Monty103/MSBE_v3/hardware/kicad/ver_1.0/MSBE_V3.kicad_sch

## KiCad design hardware/kicad/ver_1.0/MSBE_V3.kicad_sch (2026-07-17)

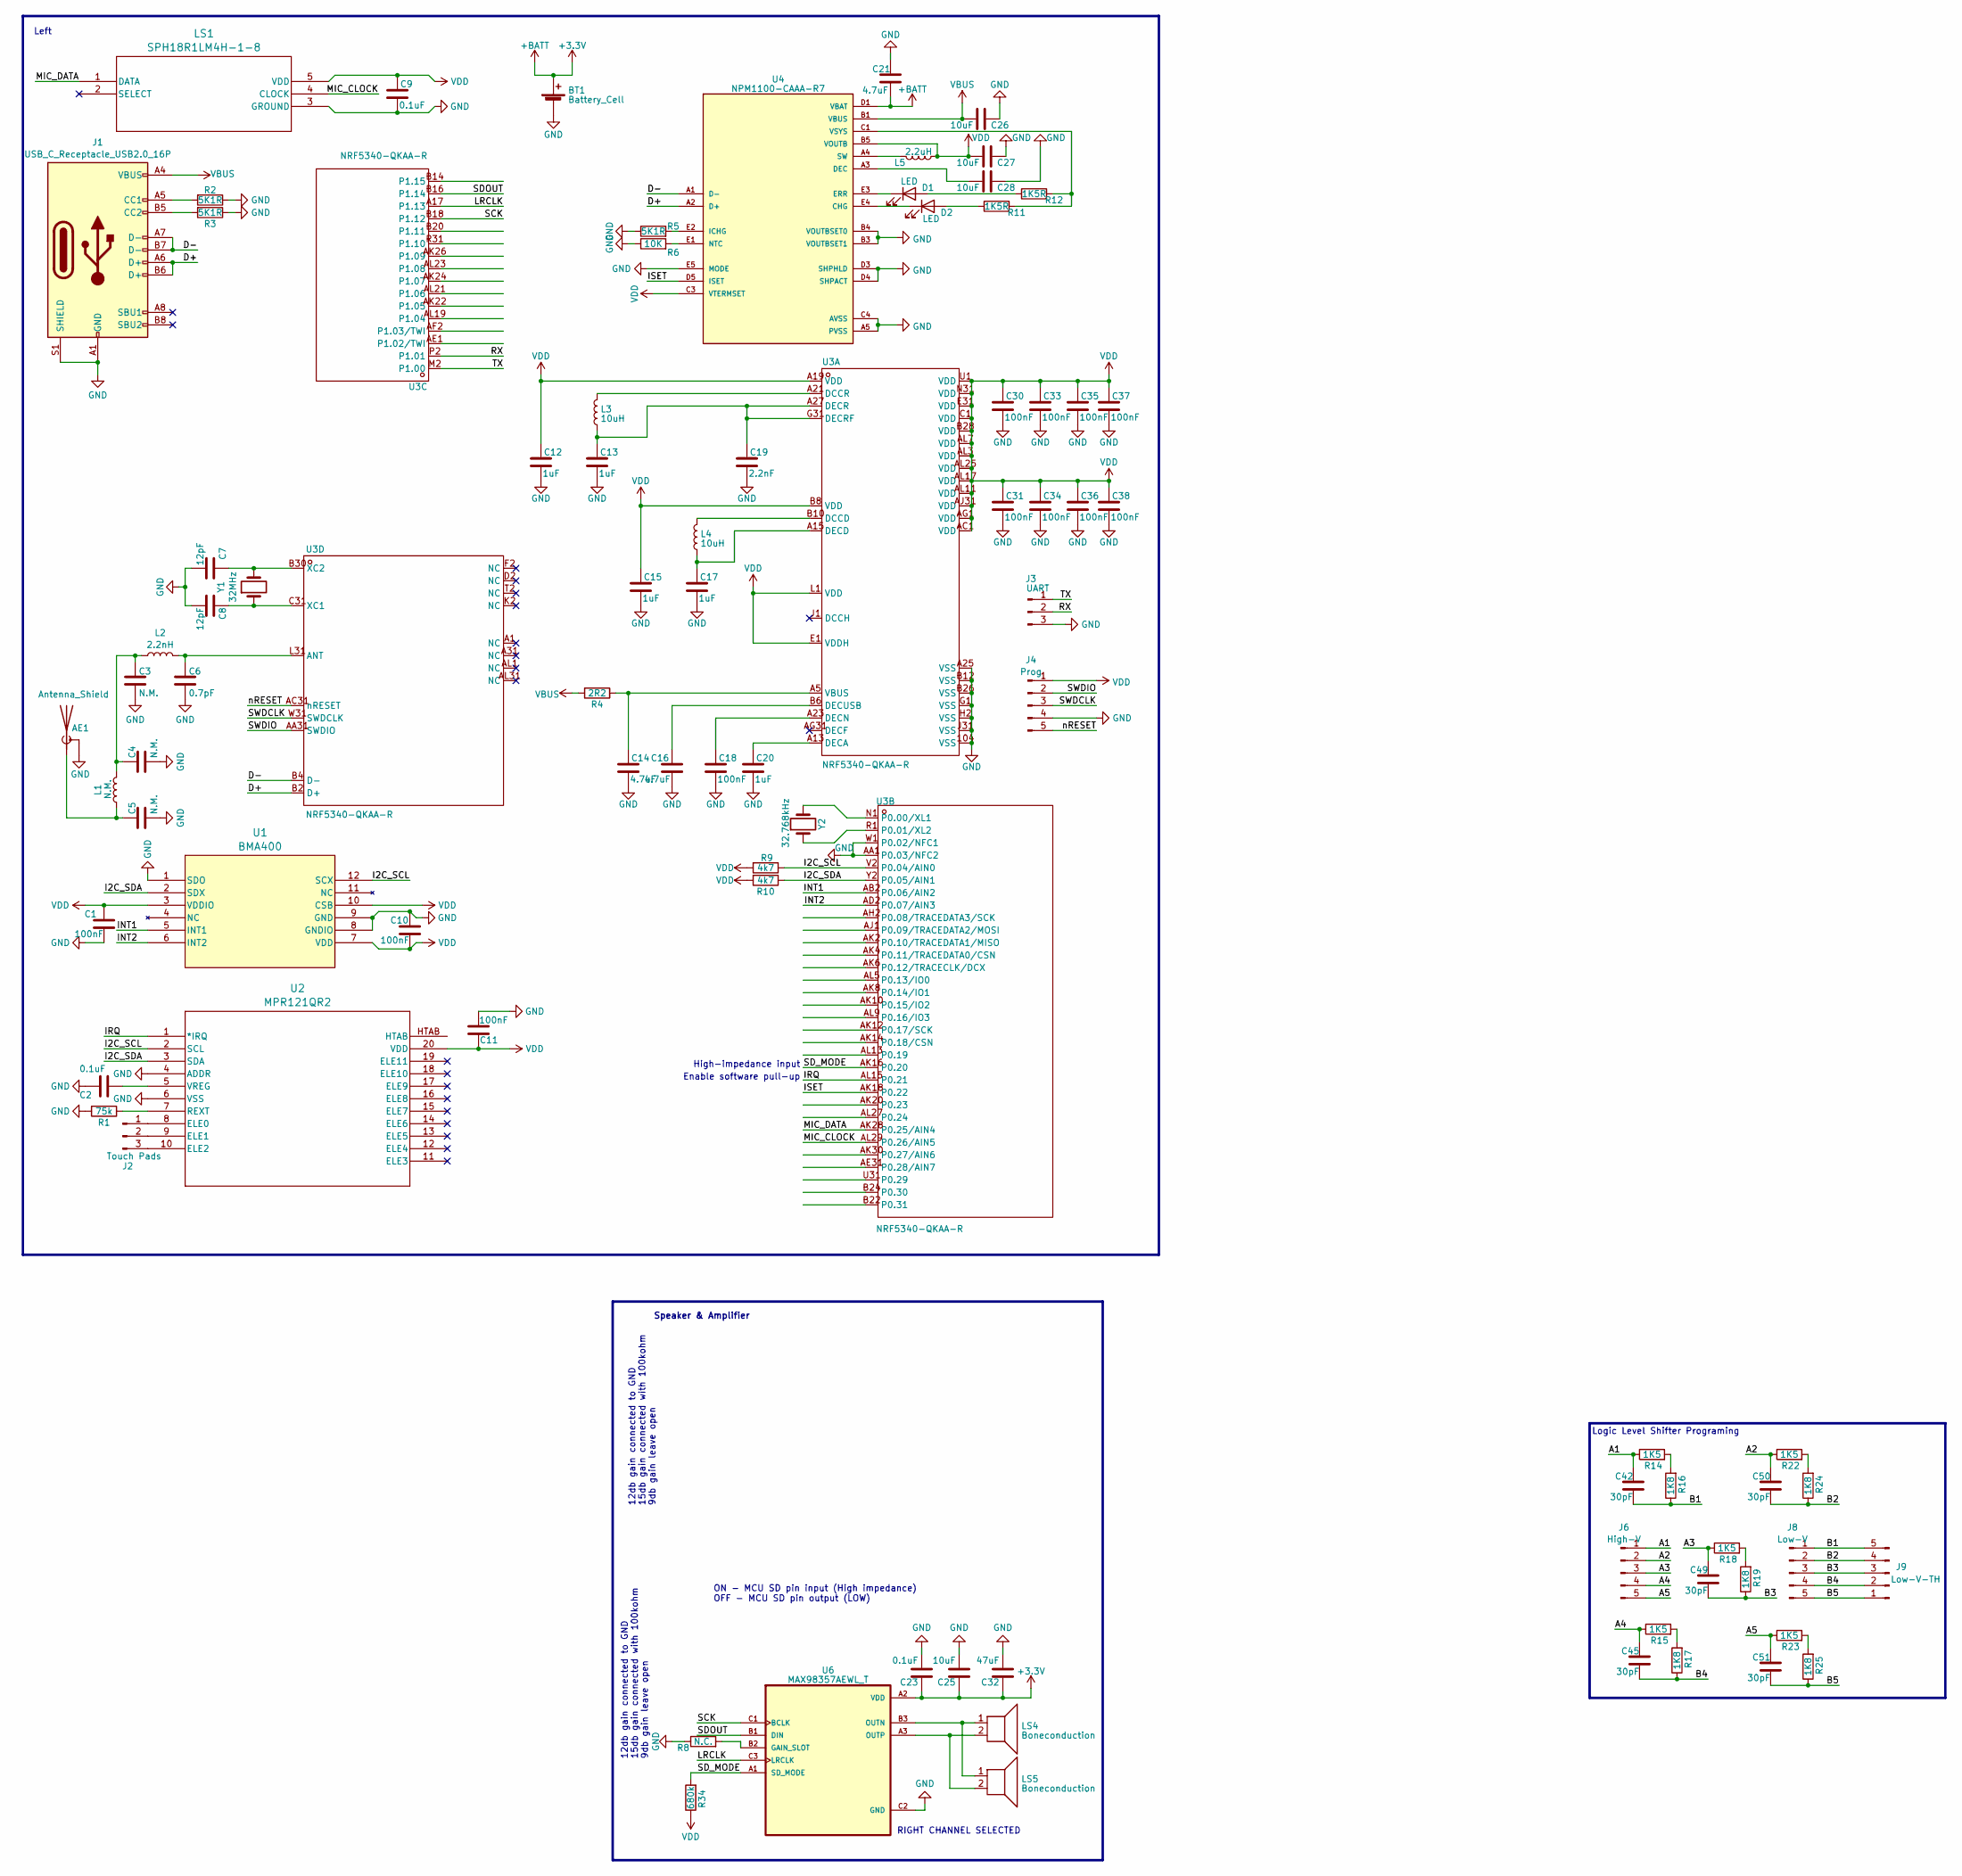
[picture p4: schematic MSBE_V3.kicad_sch]

Parts:
AE1: Antenna_Shield; Texas_SWRA117D_2.4GHz_Left
BT1: Battery_Cell; Pad_3Pin_1.5x0.8mm
C1, C10, C11, C18, C30, C31, C33, C34, C35, C36, C37, C38: 100nF; C_0603_1608Metric
C2, C9, C23: 0.1uF; C_0603_1608Metric
C3, C4, C5: N.M.; C_0603_1608Metric
C6: 0.7pF; C_0603_1608Metric
C7, C8: 12pF; C_0603_1608Metric
C12, C13, C15, C17, C20: 1uF; C_0603_1608Metric
C14, C16, C21: 4.7uF; C_0603_1608Metric
C19: 2.2nF; C_0603_1608Metric
C25, C26, C27, C28: 10uF; C_0603_1608Metric
C32: 47uF; C_0603_1608Metric
C42, C45, C49, C50, C51: 30pF; C_0603_1608Metric
D1, D2: LED; LED_0603_1608Metric
J1: USB_C_Receptacle_USB2.0_16P; USB_C_Receptacle_GCT_USB4110
J2: Touch Pads; Pad_3Pin_1.5x0.8mm
J3: UART; Pad_3Pin_1.5x0.8mm
J4: Prog; Pad_prog_4Pad
J6: High-V; Pad_prog_4Pad
J8: Low-V; Pad_prog_4Pad
J9: Low-V-TH; PinHeader_1x05_P2.54mm_Vertical
L1: N.M.; L_0603_1608Metric
L2: 2.2nH; L_0603_1608Metric
L3, L4: 10uH; L_0603_1608Metric
L5: 2.2uH; L_0603_1608Metric
LS1: SPH18R1LM4H-1-8; MIC_SPH18R1LM4H_KNO
LS4, LS5: Boneconduction; Pad_2Pin_1.5x0.8mm
R1: 75k; R_0603_1608Metric
R2, R3, R5: 5K1R; R_0603_1608Metric
R4: 2R2; R_0603_1608Metric
R6: 10K; R_0603_1608Metric
R8: N.C.; R_0603_1608Metric
R9, R10: 4k7; R_0603_1608Metric
R11, R12: 1K5R; R_0603_1608Metric
R14, R15, R18, R22, R23: 1K5; R_0603_1608Metric
R16, R17, R19, R24, R25: 1K8; R_0603_1608Metric
R34: 680k; R_0603_1608Metric
U1: BMA400; QFN_BMA400_BOS
U2: MPR121QR2; MPR121
U3: NRF5340-QKAA-R; NRF5340; VOLTAGE - SUPPLY 1.7V~5.5V; MANUFACTURER PART NRF5340-QKAA-R; LCSC PART NAME 宽电压范围、多通信协议支持的无线微控制器
U4: NPM1100-CAAA-R7; NPM1100-CAAA-BGA25C40P5X5_207X207X52N
U6: MAX98357AEWL_T; MAX98357A_BGA9N40P3X3_134X143X69N
Y1: 32MHz; ECS-160-10-37-JTN-TR_ECS
Y2: 32.768kHz; Crystal_24MHz-ECS-240-12-37B-CKY-TR

Connections:
+3.3V: BT1.1 (+), C21.2, C23.1, C25.1, C32.1, U4.D1 (VBAT), U4.D2 (VBAT), U6.A2 (VDD)
A1: C42.1, J6.1, R14.1
A2: C50.1, J6.2, R22.1
A3: C49.1, J6.3, R18.1
A4: C45.1, J6.4, R15.1
A5: C51.1, J6.5, R23.1
B1: C42.2, J8.1, J9.5, R16.1
B2: C50.2, J8.2, J9.4, R24.1
B3: C49.2, J8.3, J9.3, R19.1
B4: C45.2, J8.4, J9.2, R17.1
B5: C51.2, J8.5, J9.1, R25.1
D+: J1.A6 (D+), J1.B6 (D+), U3.B2 (D+), U4.A2 (D+)
D-: J1.A7 (D-), J1.B7 (D-), U3.B4 (D-), U4.A1 (D-)
GND: AE1.2 (Shield), BT1.2 (-), C1.2, C2.2, C3.2, C4.2, C5.2, C6.2, C7.2, C8.2, C9.2, C10.1, C11.2, C12.2, C13.2, C14.2, C15.2, C16.2, C17.2, C18.2, C19.2, C20.2, C21.1, C23.2, C25.2, C26.1, C27.1, C28.1, C30.2, C31.2, C32.2, C33.2, C34.2, C35.2, C36.2, C37.2, C38.2, J1.A1 (GND), J1.A12 (GND), J1.B1 (GND), J1.B12 (GND), J1.S1 (SHIELD), J3.3, J4.4, LS1.3 (GROUND), R1.2, R2.1, R3.1, R5.1, R6.1, R8.1, U1.1 (SDO), U1.8 (GNDIO), U1.9 (GND), U2.4 (ADDR), U2.6 (VSS), U3.104 (VSS), U3.A25 (VSS), U3.AA1 (P0.03/NFC2), U3.B12 (VSS), U3.B26 (VSS), U3.G1 (VSS), U3.H2 (VSS), U3.J31 (VSS), U3.W1 (P0.02/NFC1), U4.A5 (PVSS), U4.B3 (VOUTBSET1), U4.B4 (VOUTBSET0), U4.C4 (AVSS), U4.C5 (AVSS), U4.D3 (SHPHLD), U4.D4 (SHPACT), U4.E5 (MODE), U6.C2 (GND)
I2C_SCL: R9.1, U1.12 (SCX), U2.2 (SCL), U3.V2 (P0.04/AIN0)
I2C_SDA: R10.1, U1.2 (SDX), U2.3 (SDA), U3.Y2 (P0.05/AIN1)
INT1: U1.5 (INT1), U3.AB2 (P0.06/AIN2)
INT2: U1.6 (INT2), U3.AD2 (P0.07/AIN3)
IRQ: U2.1 (*IRQ), U3.AL15 (P0.21)
ISET: U3.AK18 (P0.22), U4.D5 (ISET)
LRCLK: U3.A17 (P1.13), U6.C3 (LRCLK)
MIC_CLOCK: LS1.4 (CLOCK), U3.AL29 (P0.26/AIN5)
MIC_DATA: LS1.1 (DATA), U3.AK28 (P0.25/AIN4)
unnamed: AE1.1 (A), C5.1, L1.1
unnamed: C2.1, U2.5 (VREG)
unnamed: C3.1, C4.1, L1.2, L2.1
unnamed: C6.1, L2.2, U3.L31 (ANT)
unnamed: C7.1, U3.B30 (XC2), Y1.2
unnamed: C8.1, U3.C31 (XC1), Y1.1
unnamed: C13.1, C19.1, L3.1, U3.A27 (DECR), U3.G31 (DECRF)
unnamed: C14.1, R4.1, U3.A5 (VBUS)
unnamed: C16.1, U3.B6 (DECUSB)
unnamed: C17.1, L4.1, U3.A15 (DECD)
unnamed: C18.1, U3.A23 (DECN)
unnamed: C20.1, U3.A13 (DECA)
unnamed: C28.2, U4.A3 (DEC)
unnamed: D1.1 (K), U4.E3 (ERR)
unnamed: D1.2 (A), R12.1
unnamed: D2.1 (K), U4.E4 (CHG)
unnamed: D2.2 (A), R11.1
unnamed: J1.A5 (CC1), R2.2
unnamed: J1.B5 (CC2), R3.2
unnamed: J2.1, U2.8 (ELE0)
unnamed: J2.2, U2.9 (ELE1)
unnamed: J2.3, U2.10 (ELE2)
unnamed: L3.2, U3.A21 (DCCR)
unnamed: L4.2, U3.B10 (DCCD)
unnamed: L5.2, U4.A4 (SW)
unnamed: LS4.1, LS5.1, U6.B3 (OUTN)
unnamed: LS4.2, LS5.2, U6.A3 (OUTP)
unnamed: R1.1, U2.7 (REXT)
unnamed: R5.2, U4.E2 (ICHG)
unnamed: R6.2, U4.E1 (NTC)
unnamed: R8.2, U6.B2 (GAIN_SLOT)
unnamed: R11.2, R12.2, U4.C1 (VSYS), U4.C2 (VSYS)
unnamed: R14.2, R16.2
unnamed: R15.2, R17.2
unnamed: R18.2, R19.2
unnamed: R22.2, R24.2
unnamed: R23.2, R25.2
unnamed: U3.N1 (P0.00/XL1), Y2.2
unnamed: U3.R1 (P0.01/XL2), Y2.1
RX: J3.2, U3.P2 (P1.01)
SCK: U3.B18 (P1.12), U6.C1 (BCLK)
SDOUT: U3.B16 (P1.14), U6.B1 (DIN)
SD_MODE: R34.2, U3.AK16 (P0.20), U6.A1 (SD_MODE)
SWDCLK: J4.3, U3.W31 (SWDCLK)
SWDIO: J4.2, U3.AA31 (SWDIO)
TX: J3.1, U3.M2 (P1.00)
VBUS: C26.2, J1.A4 (VBUS), J1.A9 (VBUS), J1.B4 (VBUS), J1.B9 (VBUS), R4.2, U4.B1 (VBUS), U4.B2 (VBUS)
VDD: C1.1, C9.1, C10.2, C11.1, C12.1, C15.1, C27.2, C30.1, C31.1, C33.1, C34.1, C35.1, C36.1, C37.1, C38.1, J4.1, L5.1, LS1.5 (VDD), R9.2, R10.2, R34.1, U1.3 (VDDIO), U1.7 (VDD), U1.10 (CSB), U2.20 (VDD), U3.A19 (VDD), U3.AC1 (VDD), U3.AG1 (VDD), U3.AJ31 (VDD), U3.AL3 (VDD), U3.AL7 (VDD), U3.AL11 (VDD), U3.AL17 (VDD), U3.AL25 (VDD), U3.B8 (VDD), U3.B28 (VDD), U3.C1 (VDD), U3.E1 (VDDH), U3.E31 (VDD), U3.L1 (VDD), U3.N31 (VDD), U3.U1 (VDD), U4.B5 (VOUTB), U4.C3 (VTERMSET)
nRESET: J4.5, U3.AC31 (nRESET)

Notes on the sheet:
ON - MCU SD pin input (High impedance) OFF - MCU SD pin output (LOW)
High-impedance input
Enable software pull-up
RIGHT CHANNEL SELECTED
Speaker & Amplifier
Left
12db gain connected to GND 15db gain connected with 100kohm 9db gain leave open
Logic Level Shifter Programing
